apuder/PocketTRS/main/splash.cpp

#include "splash.h"
#include "trs_screen.h"
#include "settings.h"
#include <cstring>


extern const unsigned char splash[1024];

void show_splash()
{
  ScreenBuffer* screenBuffer = new ScreenBuffer(MODE_TEXT_64x16);
  if (settingsSplashScreen.hideSplashScreen()) {
    memset(screenBuffer->getBuffer(), ' ', 1024);
  } else {
    memcpy(screenBuffer->getBuffer(), splash, 1024);
  }
  trs_screen.push(screenBuffer);
  trs_screen.refresh();
}

//----------------------------------------------------------------

static const char* KEY_SPLASH = "hide_splash";

void SettingsSplashScreen::init()
{
  uint8_t flag = nvs_get_u8(KEY_SPLASH);
  hide_splash_screen = (flag != 0);
}

bool SettingsSplashScreen::hideSplashScreen()
{
  return hide_splash_screen;
}

void SettingsSplashScreen::hideSplashScreen(bool hide)
{
  nvs_set_u8(KEY_SPLASH, hide ? 1 : 0);
  hide_splash_screen = hide;
}

SettingsSplashScreen settingsSplashScreen;

//----------------------------------------------------------------

const unsigned char splash[1024] = {
  0x80, 0x80, 0x80, 0x80, 0x80, 0x80, 0x80, 0x80,
  0x80, 0x80, 0x80, 0x80, 0x80, 0x80, 0x80, 0x80,
  0x80, 0x80, 0x80, 0x80, 0x80, 0x80, 0x80, 0x80,
  0x80, 0x80, 0x80, 0x80, 0x80, 0x80, 0x80, 0x80,
  0x80, 0xA0, 0xB0, 0xB0, 0xB0, 0xB0, 0xB0, 0xB0,
  0xB0, 0xB0, 0xB0, 0xB0, 0x90, 0x80, 0x80, 0x80,
  0x80, 0x80, 0x80, 0x80, 0x80, 0x80, 0x80, 0x80,
  0x80, 0x80, 0x80, 0x80, 0x80, 0x80, 0x80, 0x80,
  0x80, 0x80, 0x80, 0x80, 0x80, 0x80, 0x80, 0x80,
  0x80, 0x80, 0x80, 0x80, 0x80, 0x80, 0x80, 0x80,
  0x80, 0x80, 0x80, 0x80, 0xB0, 0xB0, 0xB0, 0xB8,
  0xBC, 0xBC, 0x9C, 0x8C, 0xAC, 0xBC, 0xB7, 0xB3,
  0xBB, 0xBB, 0xBC, 0xBE, 0xBD, 0xBC, 0xBE, 0x8C,
  0x8F, 0xA3, 0xB9, 0xB4, 0xAD, 0x80, 0x80, 0x80,
  0x80, 0x80, 0x80, 0x80, 0x80, 0x80, 0x80, 0x80,
  0x80, 0x80, 0x80, 0x80, 0x80, 0x80, 0x80, 0x80,
  0x80, 0x80, 0x80, 0x80, 0x80, 0x80, 0x80, 0x80,
  0xB0, 0xB0, 0xB0, 0xBC, 0xBC, 0xBC, 0xBC, 0xBC,
  0x87, 0xA3, 0xB3, 0xB3, 0xB9, 0x8C, 0x8C, 0x8C,
  0x8E, 0x83, 0x83, 0x83, 0x83, 0x83, 0x81, 0x80,
  0x80, 0x80, 0x80, 0xAF, 0xBF, 0xBD, 0x88, 0xBE,
  0xBF, 0xBF, 0xBF, 0xBF, 0xAA, 0x80, 0x80, 0x80,
  0x80, 0x80, 0x80, 0x80, 0x80, 0x80, 0x80, 0x80,
  0x80, 0x80, 0x80, 0x80, 0x80, 0x80, 0x80, 0x80,
  0x80, 0x80, 0x80, 0x80, 0x80, 0x80, 0x80, 0x80,
  0xBF, 0xBF, 0xBF, 0xBF, 0xBF, 0xBF, 0xBF, 0xBF,
  0x90, 0x82, 0xBF, 0x9F, 0x80, 0x80, 0x80, 0x80,
  0x80, 0x80, 0x80, 0x80, 0x80, 0x80, 0x80, 0x80,
  0x80, 0x80, 0x80, 0x82, 0xBF, 0xBF, 0x80, 0xBF,
  0xBF, 0x8F, 0x87, 0xB9, 0x96, 0x94, 0x80, 0x80,
  0x80, 0x80, 0x80, 0x80, 0x80, 0x80, 0x80, 0x80,
  0x80, 0x80, 0x80, 0x80, 0x80, 0x80, 0x80, 0x80,
  0x80, 0x80, 0x80, 0x80, 0x80, 0x80, 0x80, 0x80,
  0xAA, 0xBF, 0xBF, 0xBF, 0xBF, 0xBF, 0xBF, 0xBF,
  0xB5, 0x80, 0xBF, 0xBD, 0x80, 0x80, 0x80, 0x80,
  0x80, 0x80, 0x80, 0x80, 0x80, 0x80, 0x80, 0x80,
  0x80, 0x80, 0x80, 0x80, 0xAB, 0xBF, 0x95, 0xA3,
  0xB8, 0xBC, 0xBF, 0xBF, 0x95, 0xA5, 0x80, 0x80,
  0x80, 0x80, 0x80, 0x80, 0x80, 0x80, 0x80, 0x80,
  0x80, 0x80, 0x80, 0x80, 0x80, 0x80, 0x80, 0x80,
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
};
