apuder/PocketTRS/main/ui.cpp

#include "ui.h"
#include "calibrate.h"
#include "trs_io_host.h"
#include "bluetooth.h"
#include "trs_screen.h"
#include "fabgl.h"
#include <freertos/task.h>

extern "C" {
  #include <trs-lib.h>
  #include "settings.h"
}

#define MENU_CONFIGURE 0
#define MENU_CALIBRATE 1
#define MENU_STATUS 2
#define MENU_RESET 3
#define MENU_HELP 4
#define MENU_EXIT 5

static menu_item_t main_menu_items[] = {
  {MENU_CONFIGURE, "Configure"},
  //{MENU_CALIBRATE, "Calibrate Screen"},
  {MENU_STATUS, "Status"},
  {MENU_RESET, "Reset Settings"},
  {MENU_HELP, "Help"},
  {MENU_EXIT, "Exit"}
};

MENU(main_menu, "PocketTRS");

static ScreenBuffer* screenBuffer;

extern fabgl::PS2Controller PS2Controller;

static void screen_update(uint8_t* from, uint8_t* to)
{
  screenBuffer->update(from, to);
}

static char get_next_key()
{
  auto keyboard = PS2Controller.keyboard();

  while (true) {
    vTaskDelay(portTICK_PERIOD_MS);
    if (!keyboard->virtualKeyAvailable()) {
      continue;
    }
  
    bool down;
    auto vk = keyboard->getNextVirtualKey(&down);
    if (!down) {
      continue;
    }
    switch(vk) {
    case fabgl::VK_ESCAPE:
      return KEY_BREAK;
    case fabgl::VK_UP:
    case fabgl::VK_KP_UP:
      return KEY_UP;
    case fabgl::VK_DOWN:
    case fabgl::VK_KP_DOWN:
      return KEY_DOWN;
    case fabgl::VK_RIGHT:
    case fabgl::VK_KP_RIGHT:
      return KEY_RIGHT;
    case fabgl::VK_LEFT:
    case fabgl::VK_KP_LEFT:
      return KEY_LEFT;
    default:
      int c = keyboard->virtualKeyToASCII(vk);
      if (c > -1) {
        return c;
      }
      break;
    }
  }
}

void configure_pocket_trs()
{
  bool show_from_left = false;
  bool exit = false;
  uint8_t mode = trs_screen.getMode();

  screenBuffer = new ScreenBuffer(mode);
  trs_screen.push(screenBuffer);
  screenBuffer->copyBufferFrom(screenBuffer->getNext());

  ScreenBuffer* backgroundBuffer = new ScreenBuffer(mode);
  trs_screen.push(backgroundBuffer);

  set_screen(screenBuffer->getBuffer(), backgroundBuffer->getBuffer(),
	     screenBuffer->getWidth(), screenBuffer->getHeight());

  set_screen_callback(screen_update);
  set_keyboard_callback(get_next_key);
  
  while (!exit) {
    uint8_t action = menu(&main_menu, show_from_left, true);
    switch (action) {
    case MENU_CONFIGURE:
      configure();
      break;
    case MENU_CALIBRATE:
      calibrate();
      break;
    case MENU_STATUS:
      status();
      break;
    case MENU_RESET:
      if (bt_kbd_unpair()) {
        static bt_kbd_status_t bt EXT_RAM_BSS_ATTR;
        do {
          vTaskDelay(100 / portTICK_PERIOD_MS);
          bt_kbd_get_status(&bt);
        } while (bt.activity != BT_KBD_IDLE);
      }
      SettingsBase::reset();
      trs_io_host_reset_settings();
      esp_restart();
      break;
    case MENU_HELP:
      help();
      break;
    case MENU_EXIT:
    case MENU_ABORT:
      exit = true;
      break;
    }
    show_from_left = true;
  }

  // Copy original screen content of the TRS emulation
  // to the background buffer
  backgroundBuffer->copyBufferFrom(screenBuffer->getNext());
  screen_show(true);
  trs_screen.pop();
  trs_screen.pop();
}
